stteff/An-Open-Educational-RPi-Robot/docs/images/Ball_caster.png

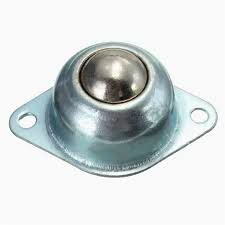
docs/images/Ball_caster.png
