stteff/An-Open-Educational-RPi-Robot/docs/images/Battery_holder.png

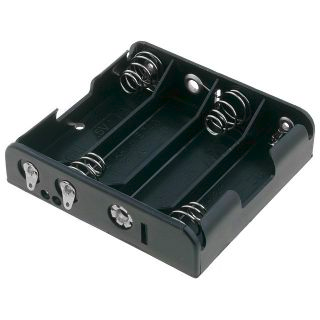
docs/images/Battery_holder.png
