stteff/An-Open-Educational-RPi-Robot/docs/images/Encoder_disk.png

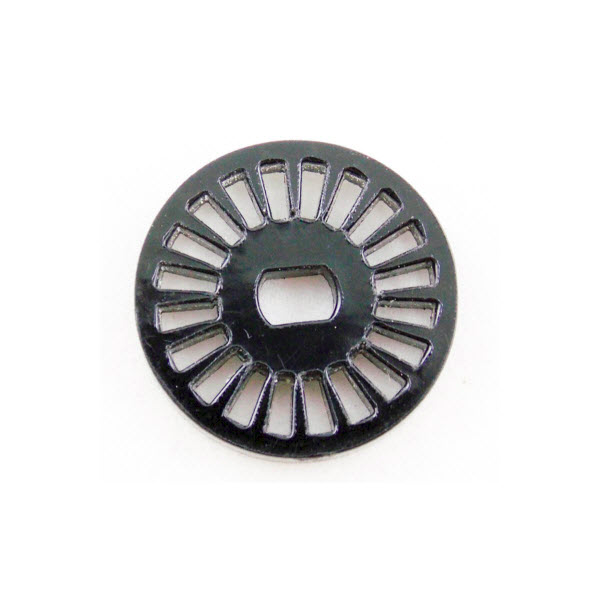
docs/images/Encoder_disk.png
