stteff/An-Open-Educational-RPi-Robot/docs/images/Servo_motor.png

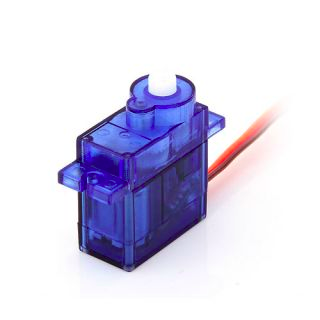
docs/images/Servo_motor.png
