stteff/An-Open-Educational-RPi-Robot/docs/images/Servo_wheel.png

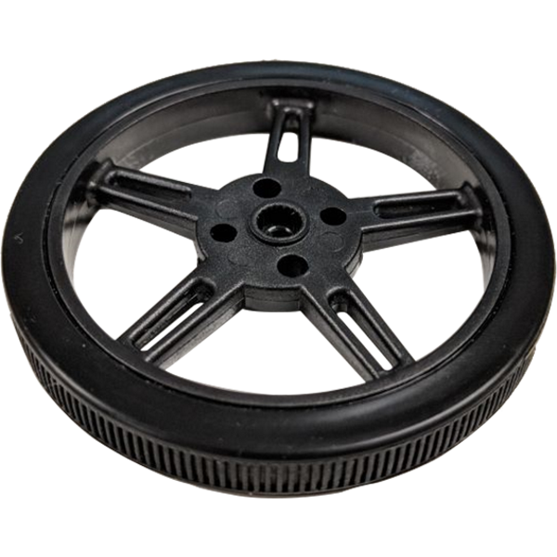
docs/images/Servo_wheel.png
